Geox644/OpenBook-E-Reader/Images/Baterie.png

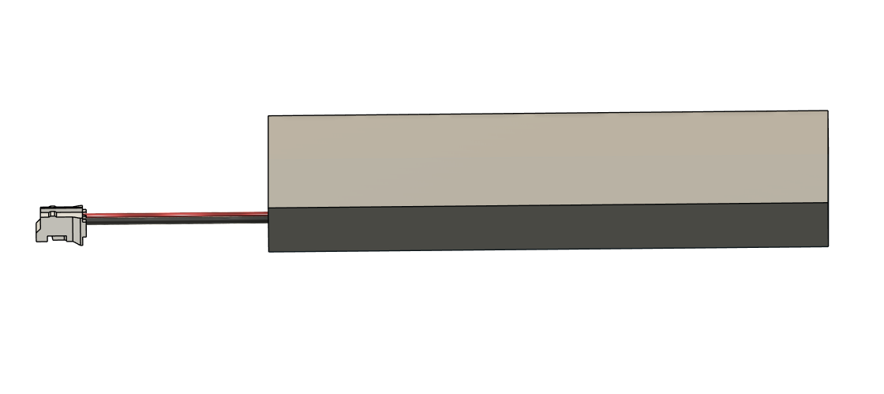
Images/Baterie.png
