Geox644/OpenBook-E-Reader/Images/Display.png

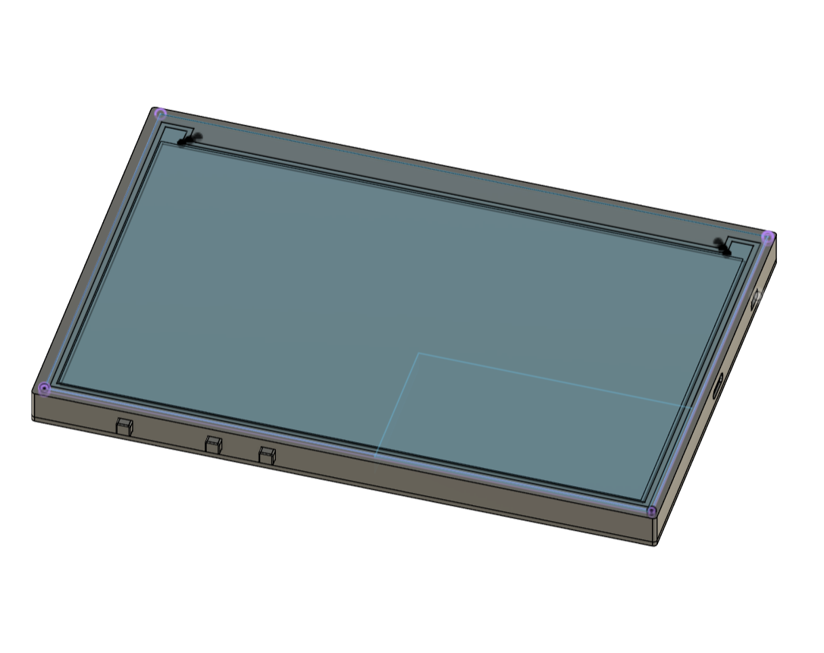
Images/Display.png
