Geox644/OpenBook-E-Reader/Images/OpenBook.png

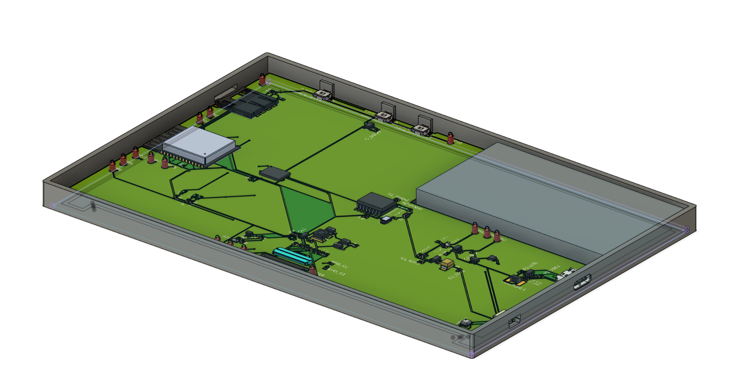
Images/OpenBook.png
