Geox644/OpenBook-E-Reader/Images/OpenBookBottomWithDisplay.png

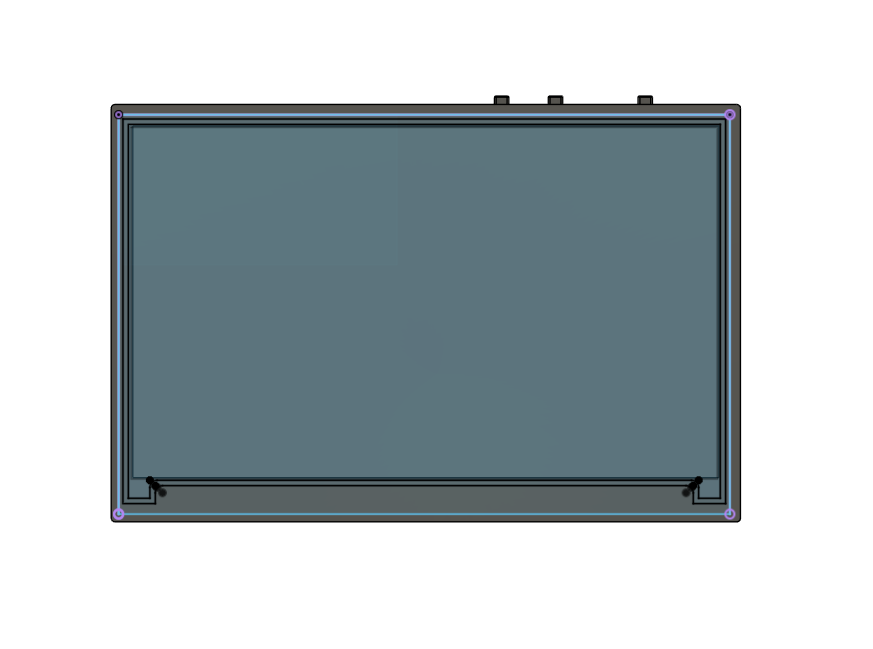
Images/OpenBookBottomWithDisplay.png
