Geox644/OpenBook-E-Reader/Images/PCB.png

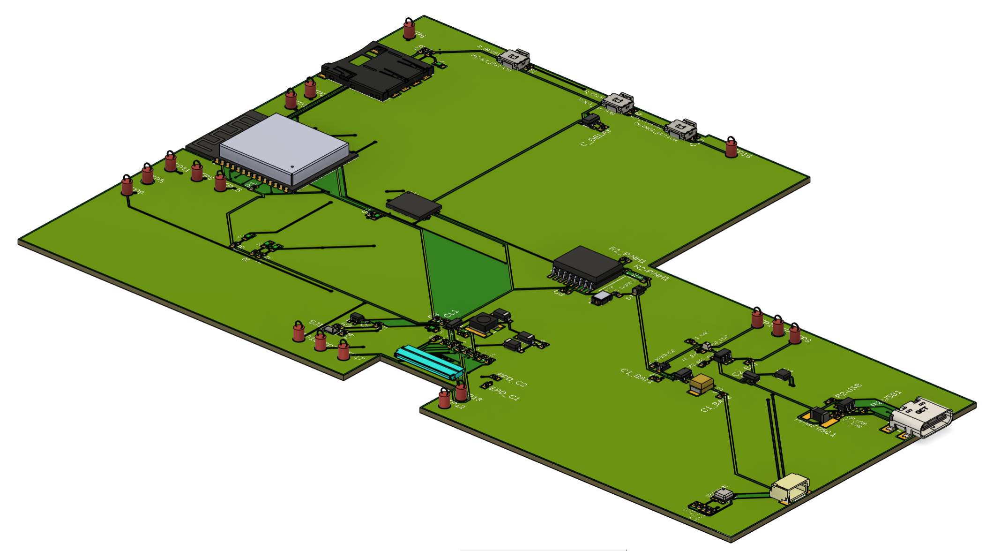
Images/PCB.png
